Jun-robot/3DPrintedMotor/発表資料等/未踏ジュニア/成果報告会/スライド19.PNG

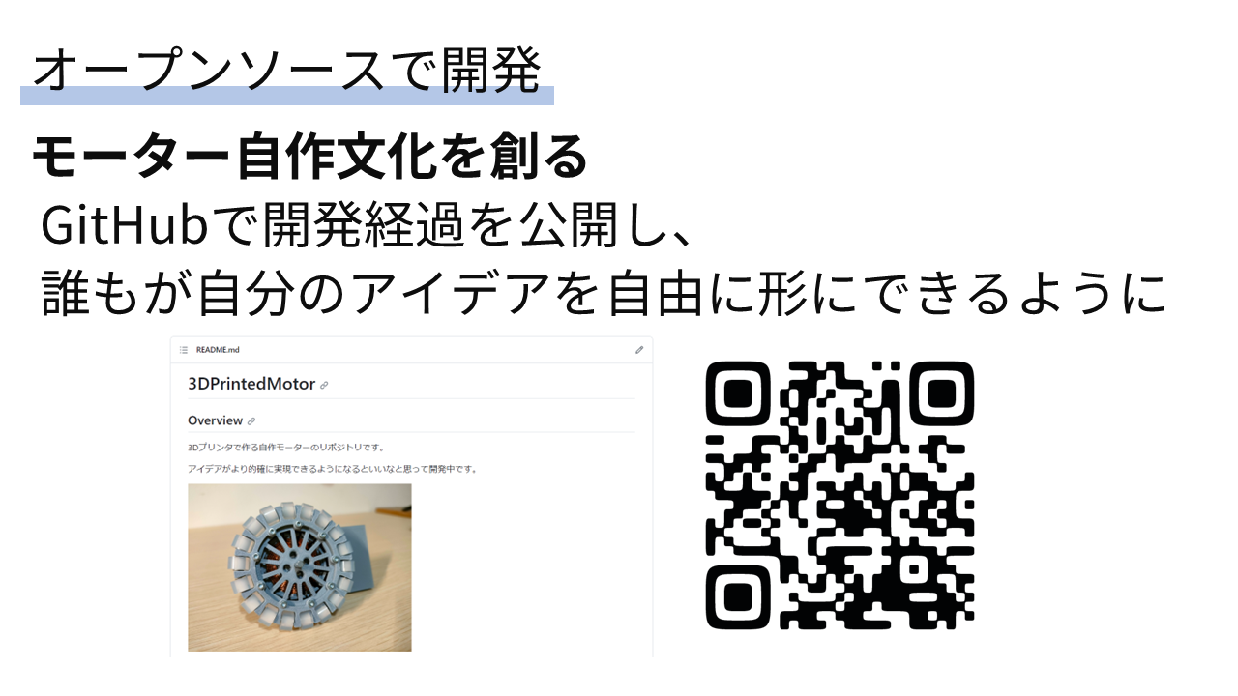
発表資料等/未踏ジュニア/成果報告会/スライド19.PNG
